nicohmje/PID-ballonplate/3MF Files/test_link.3MF

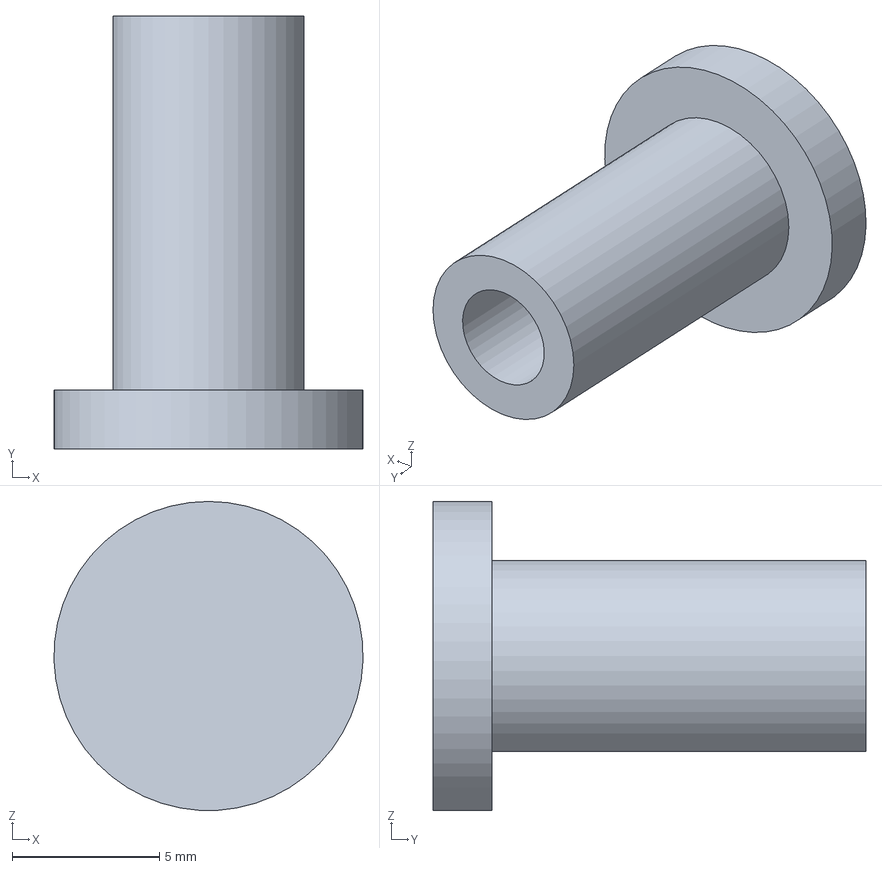
[picture p15: CAD file, 2022-06-13]
3MF Files/test_link.3MF
10.5 x 14.7 x 10.5 mm
