nicohmje/PID-ballonplate/3MF Files/Servo_bracket_proto1.3MF

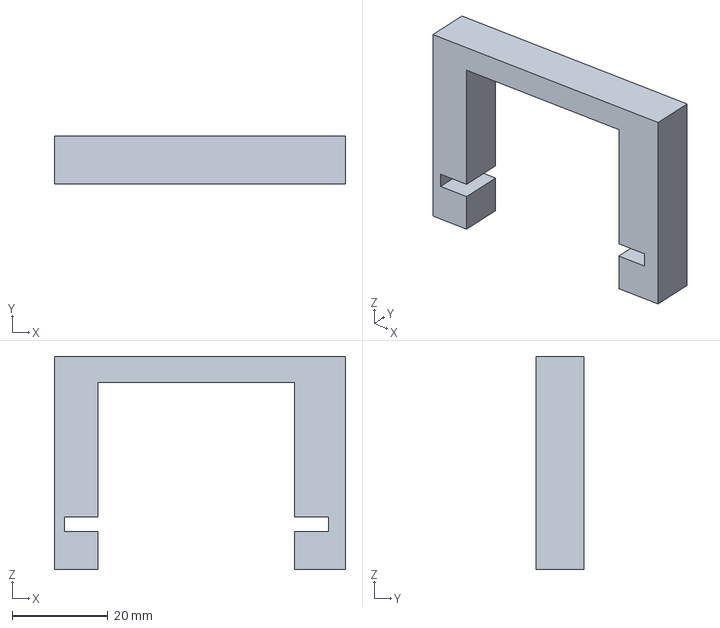
[picture p16: CAD file, 2022-06-13]
3MF Files/Servo_bracket_proto1.3MF
60.7 x 10.0 x 44.5 mm
