nicohmje/PID-ballonplate/3MF Files/Arm2_proto2.3MF

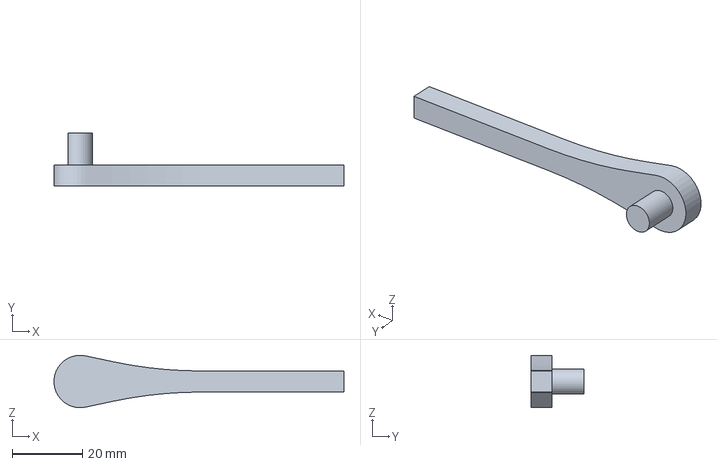
[picture p17: CAD file, 2022-06-13]
3MF Files/Arm2_proto2.3MF
82.4 x 15.0 x 14.9 mm
