nicohmje/PID-ballonplate/3MF Files/PLATEAU.3MF

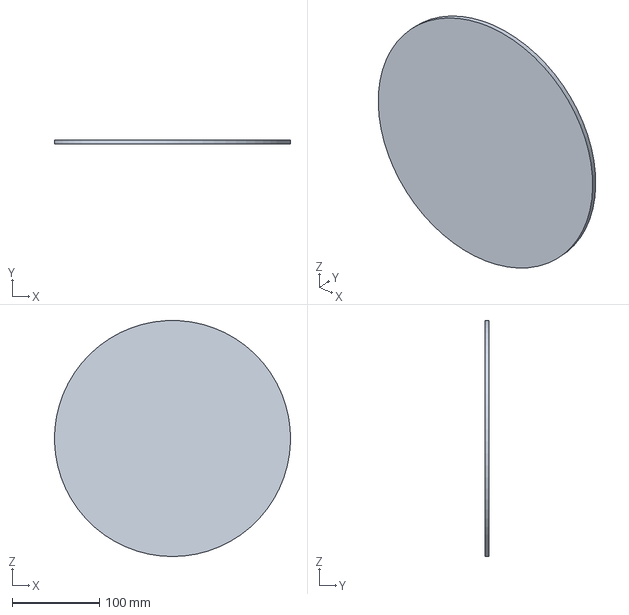
[picture p18: CAD file, 2022-06-13]
3MF Files/PLATEAU.3MF
269.9 x 5.00 x 270.0 mm
